GreatMesa/Bike-Led-Controller/Hardware/Microcontroller.kicad_sch

## KiCad design Hardware/Microcontroller.kicad_sch (2026-06-11)

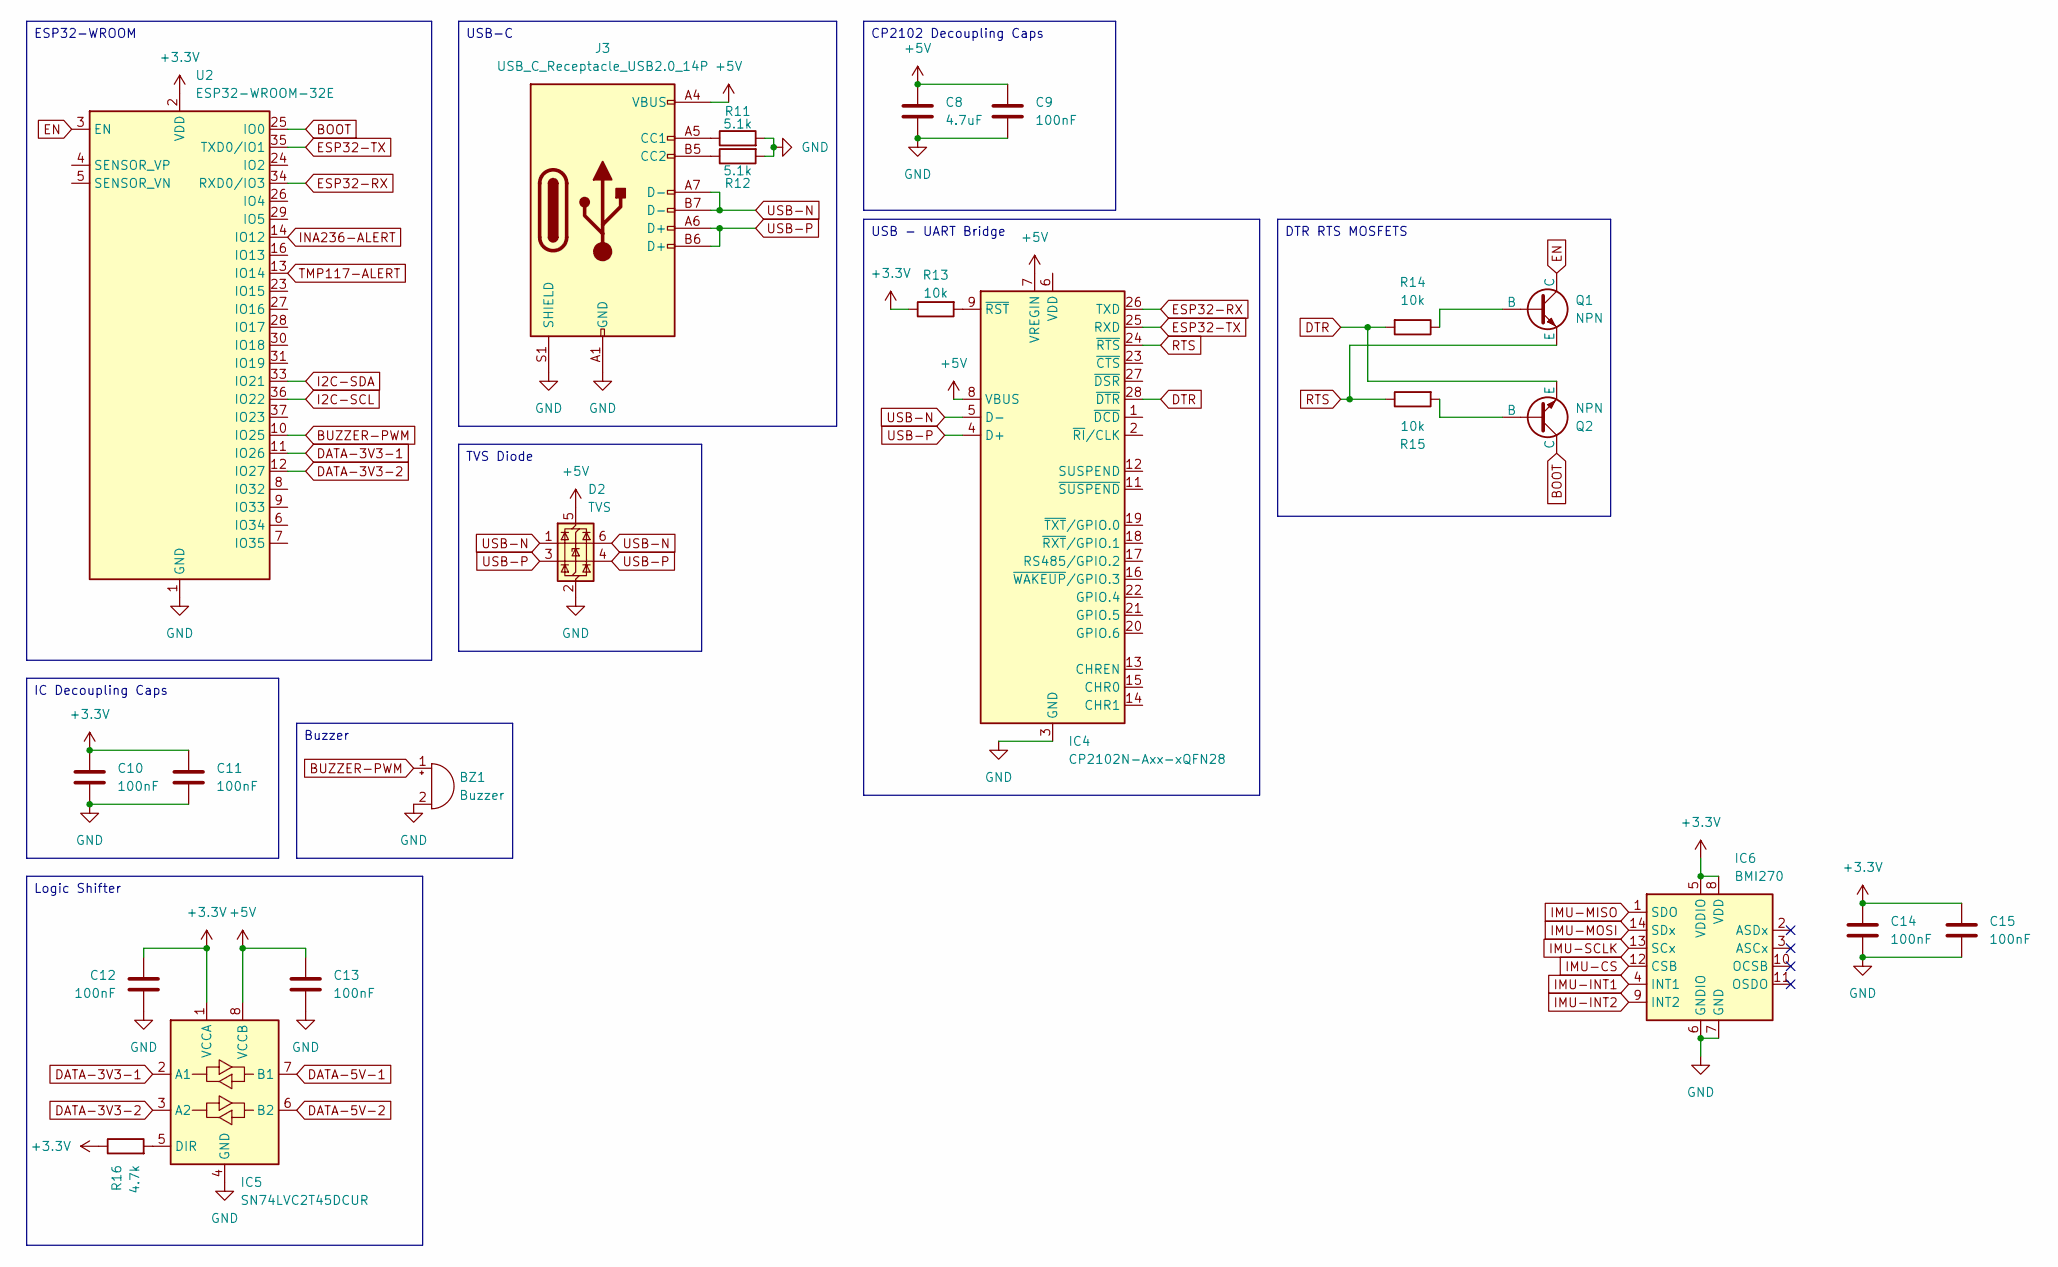
[picture p2: schematic Microcontroller.kicad_sch]

Parts:
BZ1: Buzzer; CMI97050380SMTTR
C8: 4.7uF; C_0603_1608Metric
C9, C10, C11, C12, C13, C14, C15: 100nF; C_0402_1005Metric
D2: TVS; SOT-666
IC4: CP2102N-Axx-xQFN28; QFN-28-1EP_5x5mm_P0.5mm_EP3.35x3.35mm
IC5: SN74LVC2T45DCUR; VSSOP-8_2.3x2mm_P0.5mm
IC6: BMI270; Bosch_LGA-14_3x2.5mm_P0.5mm
J3: USB_C_Receptacle_USB2.0_14P; USB_C_Receptacle_GCT_USB4105-xx-A_16P_TopMnt_Horizontal
Q1, Q2: NPN; SOT95P240X115-3N
R11, R12: 5.1k; R_0402_1005Metric
R13, R14, R15: 10k; R_0402_1005Metric
R16: 4.7k; R_0402_1005Metric
U2: ESP32-WROOM-32E

Connections:
+3.3V: C10.1, C11.1, C12.1, C14.1, C15.1, IC5.1 (VCCA), IC6.5 (VDDIO), IC6.8 (VDD), R13.1, R16.1, U2.2 (VDD)
+5V: C8.1, C9.1, C13.1, D2.5 (VBUS), IC4.7 (VREGIN), IC4.8 (VBUS), IC5.8 (VCCB), J3.A4 (VBUS), J3.A9 (VBUS), J3.B4 (VBUS), J3.B9 (VBUS)
BOOT: Q2.1 (C), U2.25 (IO0)
BUZZER-PWM: BZ1.1 (+), U2.10 (IO25)
DATA-3V3-1: IC5.2 (A1), U2.11 (IO26)
DATA-3V3-2: IC5.3 (A2), U2.12 (IO27)
DATA-5V-1: IC5.7 (B1)
DATA-5V-2: IC5.6 (B2)
DTR: IC4.28 (~DTR), Q2.3 (E), R14.2
EN: Q1.1 (C), U2.3 (EN)
ESP32-RX: IC4.26 (TXD), U2.34 (RXD0/IO3)
ESP32-TX: IC4.25 (RXD), U2.35 (TXD0/IO1)
GND: BZ1.2 (-), C8.2, C9.2, C10.2, C11.2, C12.2, C13.2, C14.2, C15.2, D2.2 (GND), IC4.3 (GND), IC4.29 (GND), IC5.4 (GND), IC6.6 (GNDIO), IC6.7 (GND), J3.A1 (GND), J3.A12 (GND), J3.B1 (GND), J3.B12 (GND), J3.S1 (SHIELD), R11.2, R12.2, U2.1 (GND), U2.15 (GND), U2.38 (GND), U2.39 (GND)
I2C-SCL: U2.36 (IO22)
I2C-SDA: U2.33 (IO21)
IMU-CS: IC6.12 (CSB)
IMU-INT1: IC6.4 (INT1)
IMU-INT2: IC6.9 (INT2)
IMU-MISO: IC6.1 (SDO)
IMU-MOSI: IC6.14 (SDx)
IMU-SCLK: IC6.13 (SCx)
INA236-ALERT: U2.14 (IO12)
unnamed: IC4.9 (~RST), R13.2
unnamed: IC5.5 (DIR), R16.2
unnamed: J3.A5 (CC1), R11.1
unnamed: J3.B5 (CC2), R12.1
unnamed: Q1.2 (B), R14.1
unnamed: Q2.2 (B), R15.2
RTS: IC4.24 (~RTS), Q1.3 (E), R15.1
TMP117-ALERT: U2.13 (IO14)
USB-N: D2.1 (I/O1), D2.6 (I/O1), IC4.5 (D-), J3.A7 (D-), J3.B7 (D-)
USB-P: D2.3 (I/O2), D2.4 (I/O2), IC4.4 (D+), J3.A6 (D+), J3.B6 (D+)

Notes on the sheet:
TVS Diode
USB-C
Logic Shifter
IC Decoupling Caps
ESP32-WROOM
USB - UART Bridge
CP2102 Decoupling Caps
DTR RTS MOSFETS
Buzzer
