GreatMesa/Bike-Led-Controller/Hardware/Power.kicad_sch

## KiCad design Hardware/Power.kicad_sch (2026-06-11)

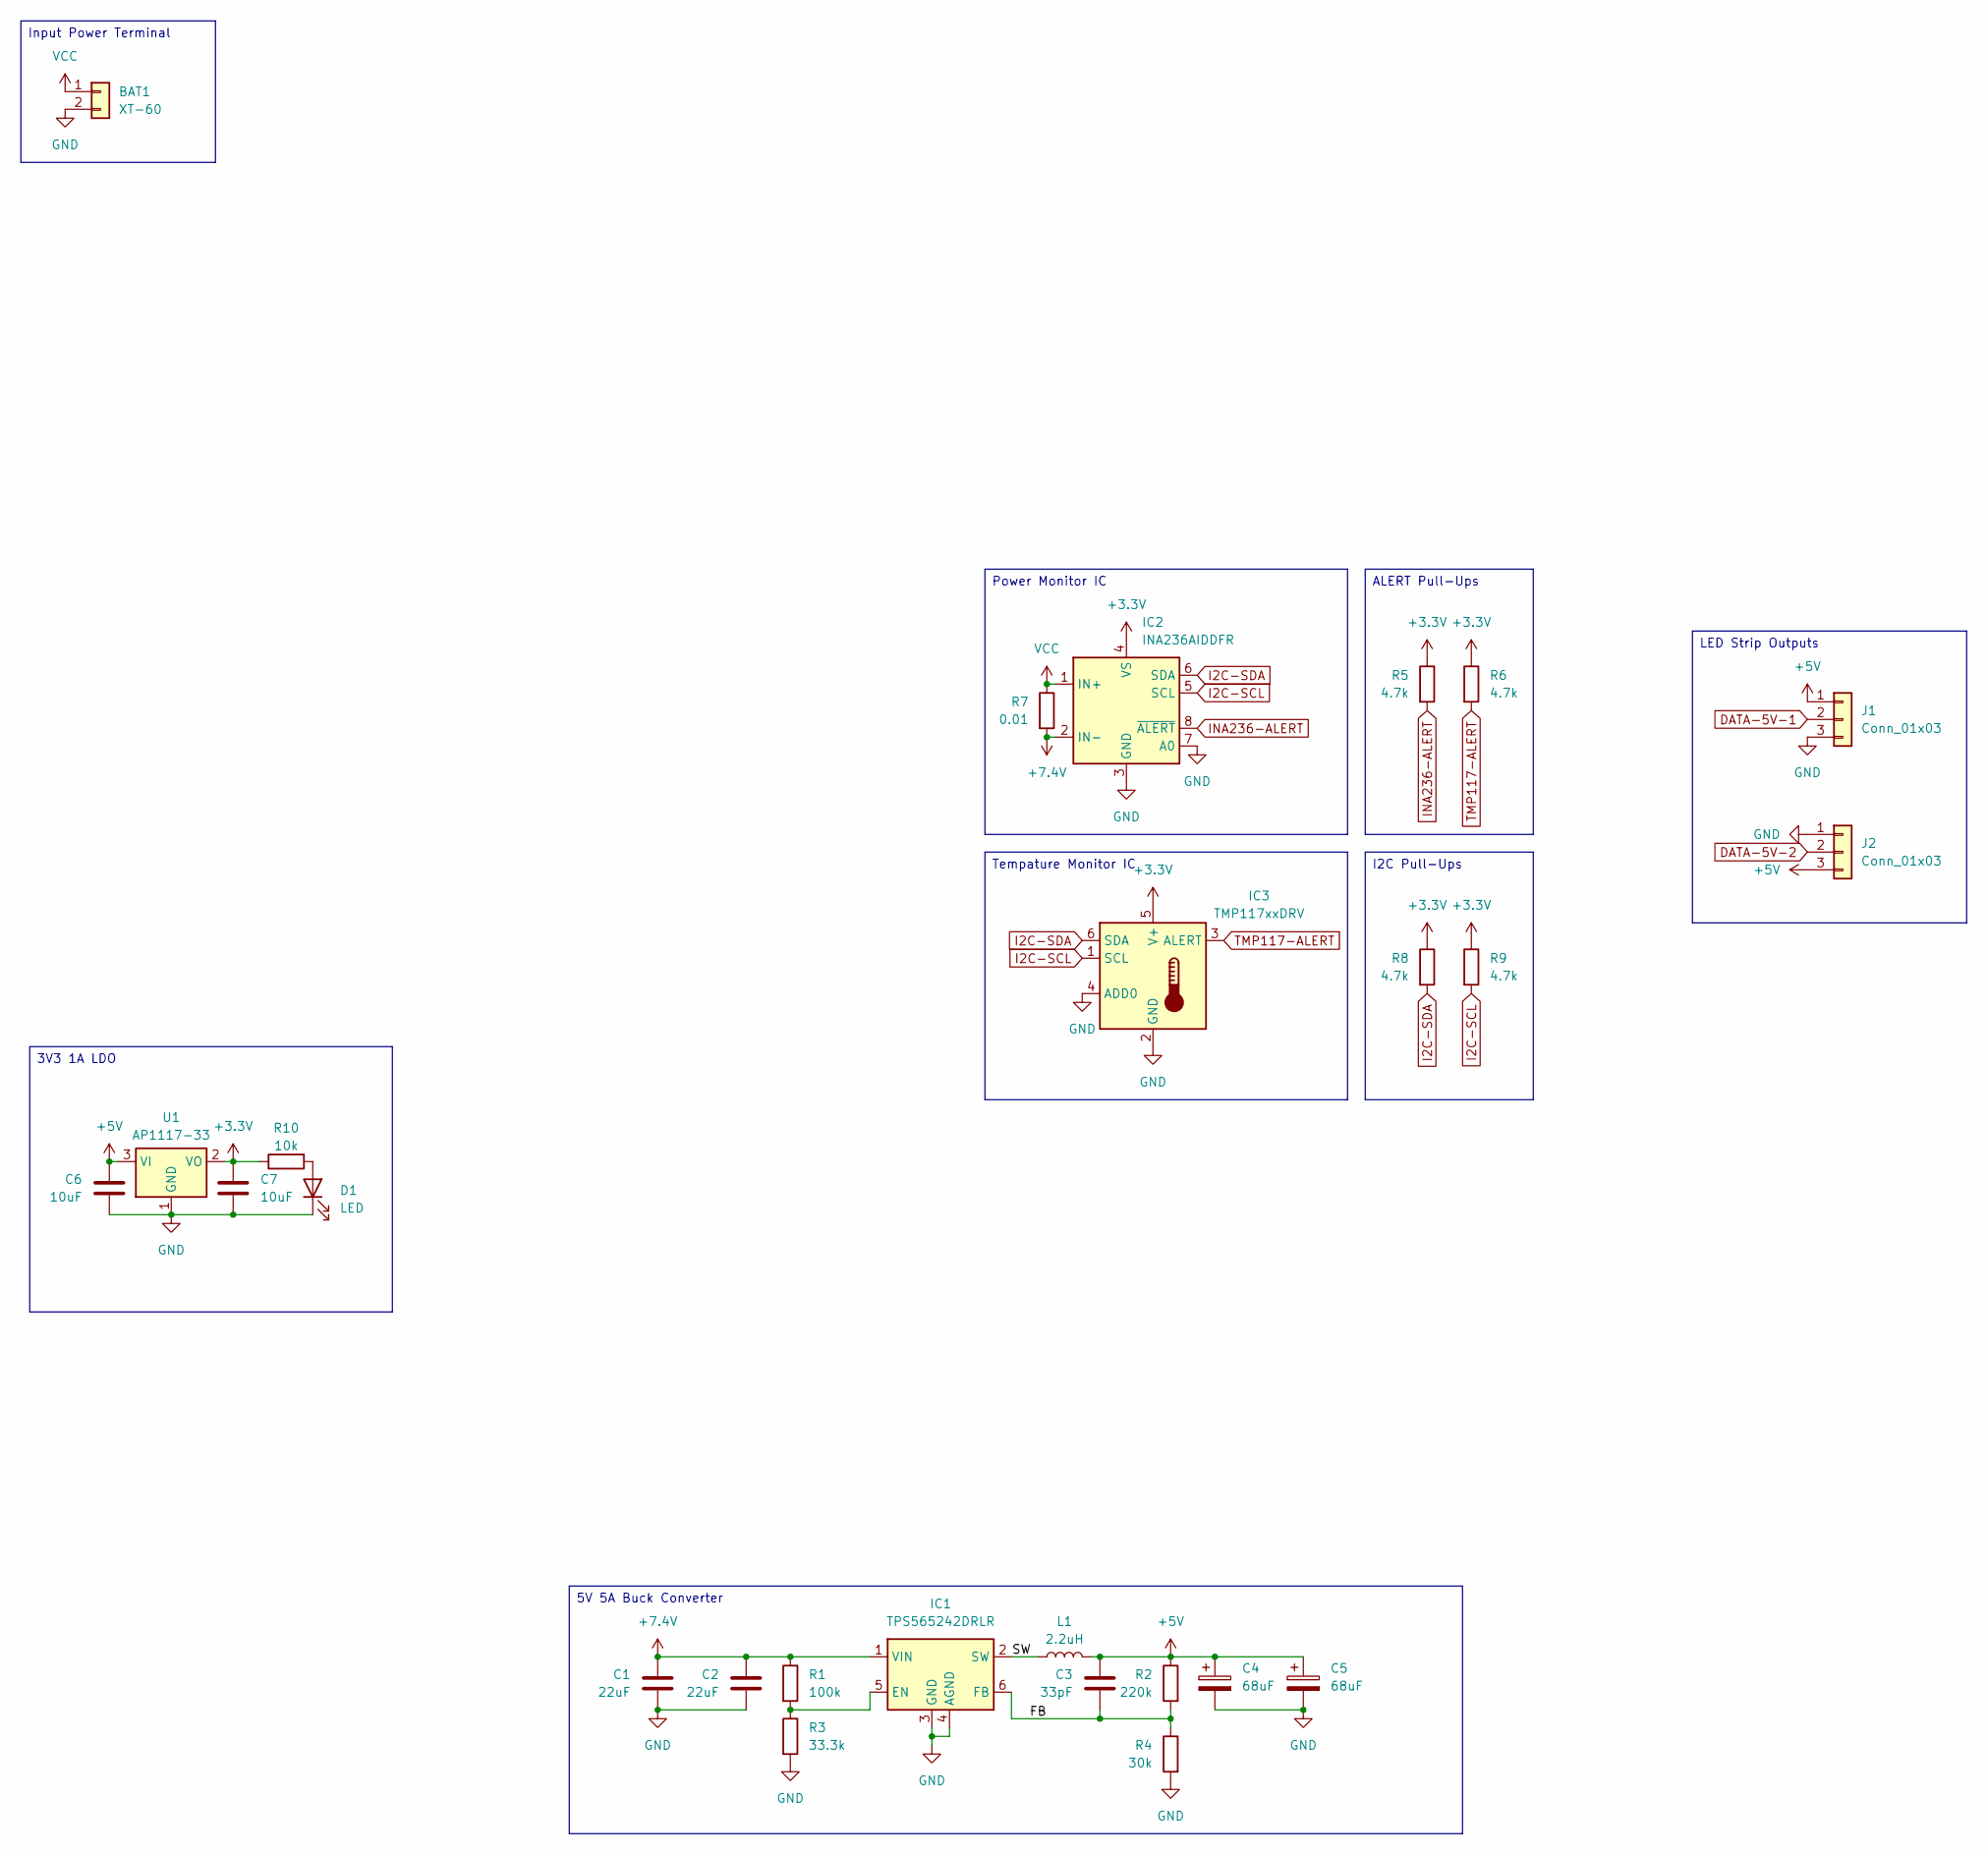
[picture p3: schematic Power.kicad_sch]

Parts:
BAT1: XT-60; AMASS_XT60-F_1x02_P7.20mm_Vertical
C1, C2: 22uF; C_0805_2012Metric
C3: 33pF; C_0402_1005Metric
C4, C5: 68uF; CP_Elec_6.3x5.8
C6, C7: 10uF; C_0805_2012Metric
D1: LED; LED_0603_1608Metric
IC1: TPS565242DRLR; SOTFL50P160X60-6N
IC2: INA236AIDDFR; SOP65P280X110-8N; Mouser Part Number 595-INA232BIDDFR
IC3: TMP117xxDRV; WSON-6-1EP_2x2mm_P0.65mm_EP1x1.6mm
J1, J2: Conn_01x03; TerminalBlock_Phoenix_MKDS-1,5-3_1x03_P5.00mm_Horizontal
L1: 2.2uH; L_Coilcraft_XAL5030-XXX
R1: 100k; R_0402_1005Metric
R2: 220k; R_0402_1005Metric
R3: 33.3k; R_0402_1005Metric
R4: 30k; R_0402_1005Metric
R5, R6, R8, R9: 4.7k; R_0402_1005Metric
R7: 0.01; R_2512_6332Metric
R10: 10k; R_0402_1005Metric
U1: AP1117-33; SOT-223-3_TabPin2

Connections:
+3.3V: C7.1, IC2.4 (VS), IC3.5 (V+), R5.1, R6.1, R8.1, R9.1, R10.1, U1.2 (VO)
+5V: C3.1, C4.1, C5.1, C6.1, J1.1, J2.3, L1.2, R2.1, U1.3 (VI)
+7.4V: C1.1, C2.1, IC1.1 (VIN), IC2.2 (IN-), R1.1, R7.2
DATA-5V-1: J1.2
DATA-5V-2: J2.2
FB: C3.2, IC1.6 (FB), R2.2, R4.1
GND: BAT1.2, C1.2, C2.2, C4.2, C5.2, C6.2, C7.2, D1.1 (K), IC1.3 (GND), IC1.4 (AGND), IC2.3 (GND), IC2.7 (A0), IC3.2 (GND), IC3.4 (ADD0), J1.3, J2.1, R3.2, R4.2, U1.1 (GND)
I2C-SCL: IC2.5 (SCL), IC3.1 (SCL), R9.2
I2C-SDA: IC2.6 (SDA), IC3.6 (SDA), R8.2
INA236-ALERT: IC2.8 (~ALERT), R5.2
unnamed: D1.2 (A), R10.2
unnamed: IC1.5 (EN), R1.2, R3.1
SW: IC1.2 (SW), L1.1
TMP117-ALERT: IC3.3 (ALERT), R6.2
VCC: BAT1.1, IC2.1 (IN+), R7.1

Notes on the sheet:
Power Monitor IC
3V3 1A LDO
I2C Pull-Ups
LED Strip Outputs
ALERT Pull-Ups
Tempature Monitor IC
Input Power Terminal
5V 5A Buck Converter
