GreatMesa/Bike-Led-Controller/Hardware/WLED Controller.kicad_sch

## KiCad design Hardware/WLED Controller.kicad_sch (2026-06-11)

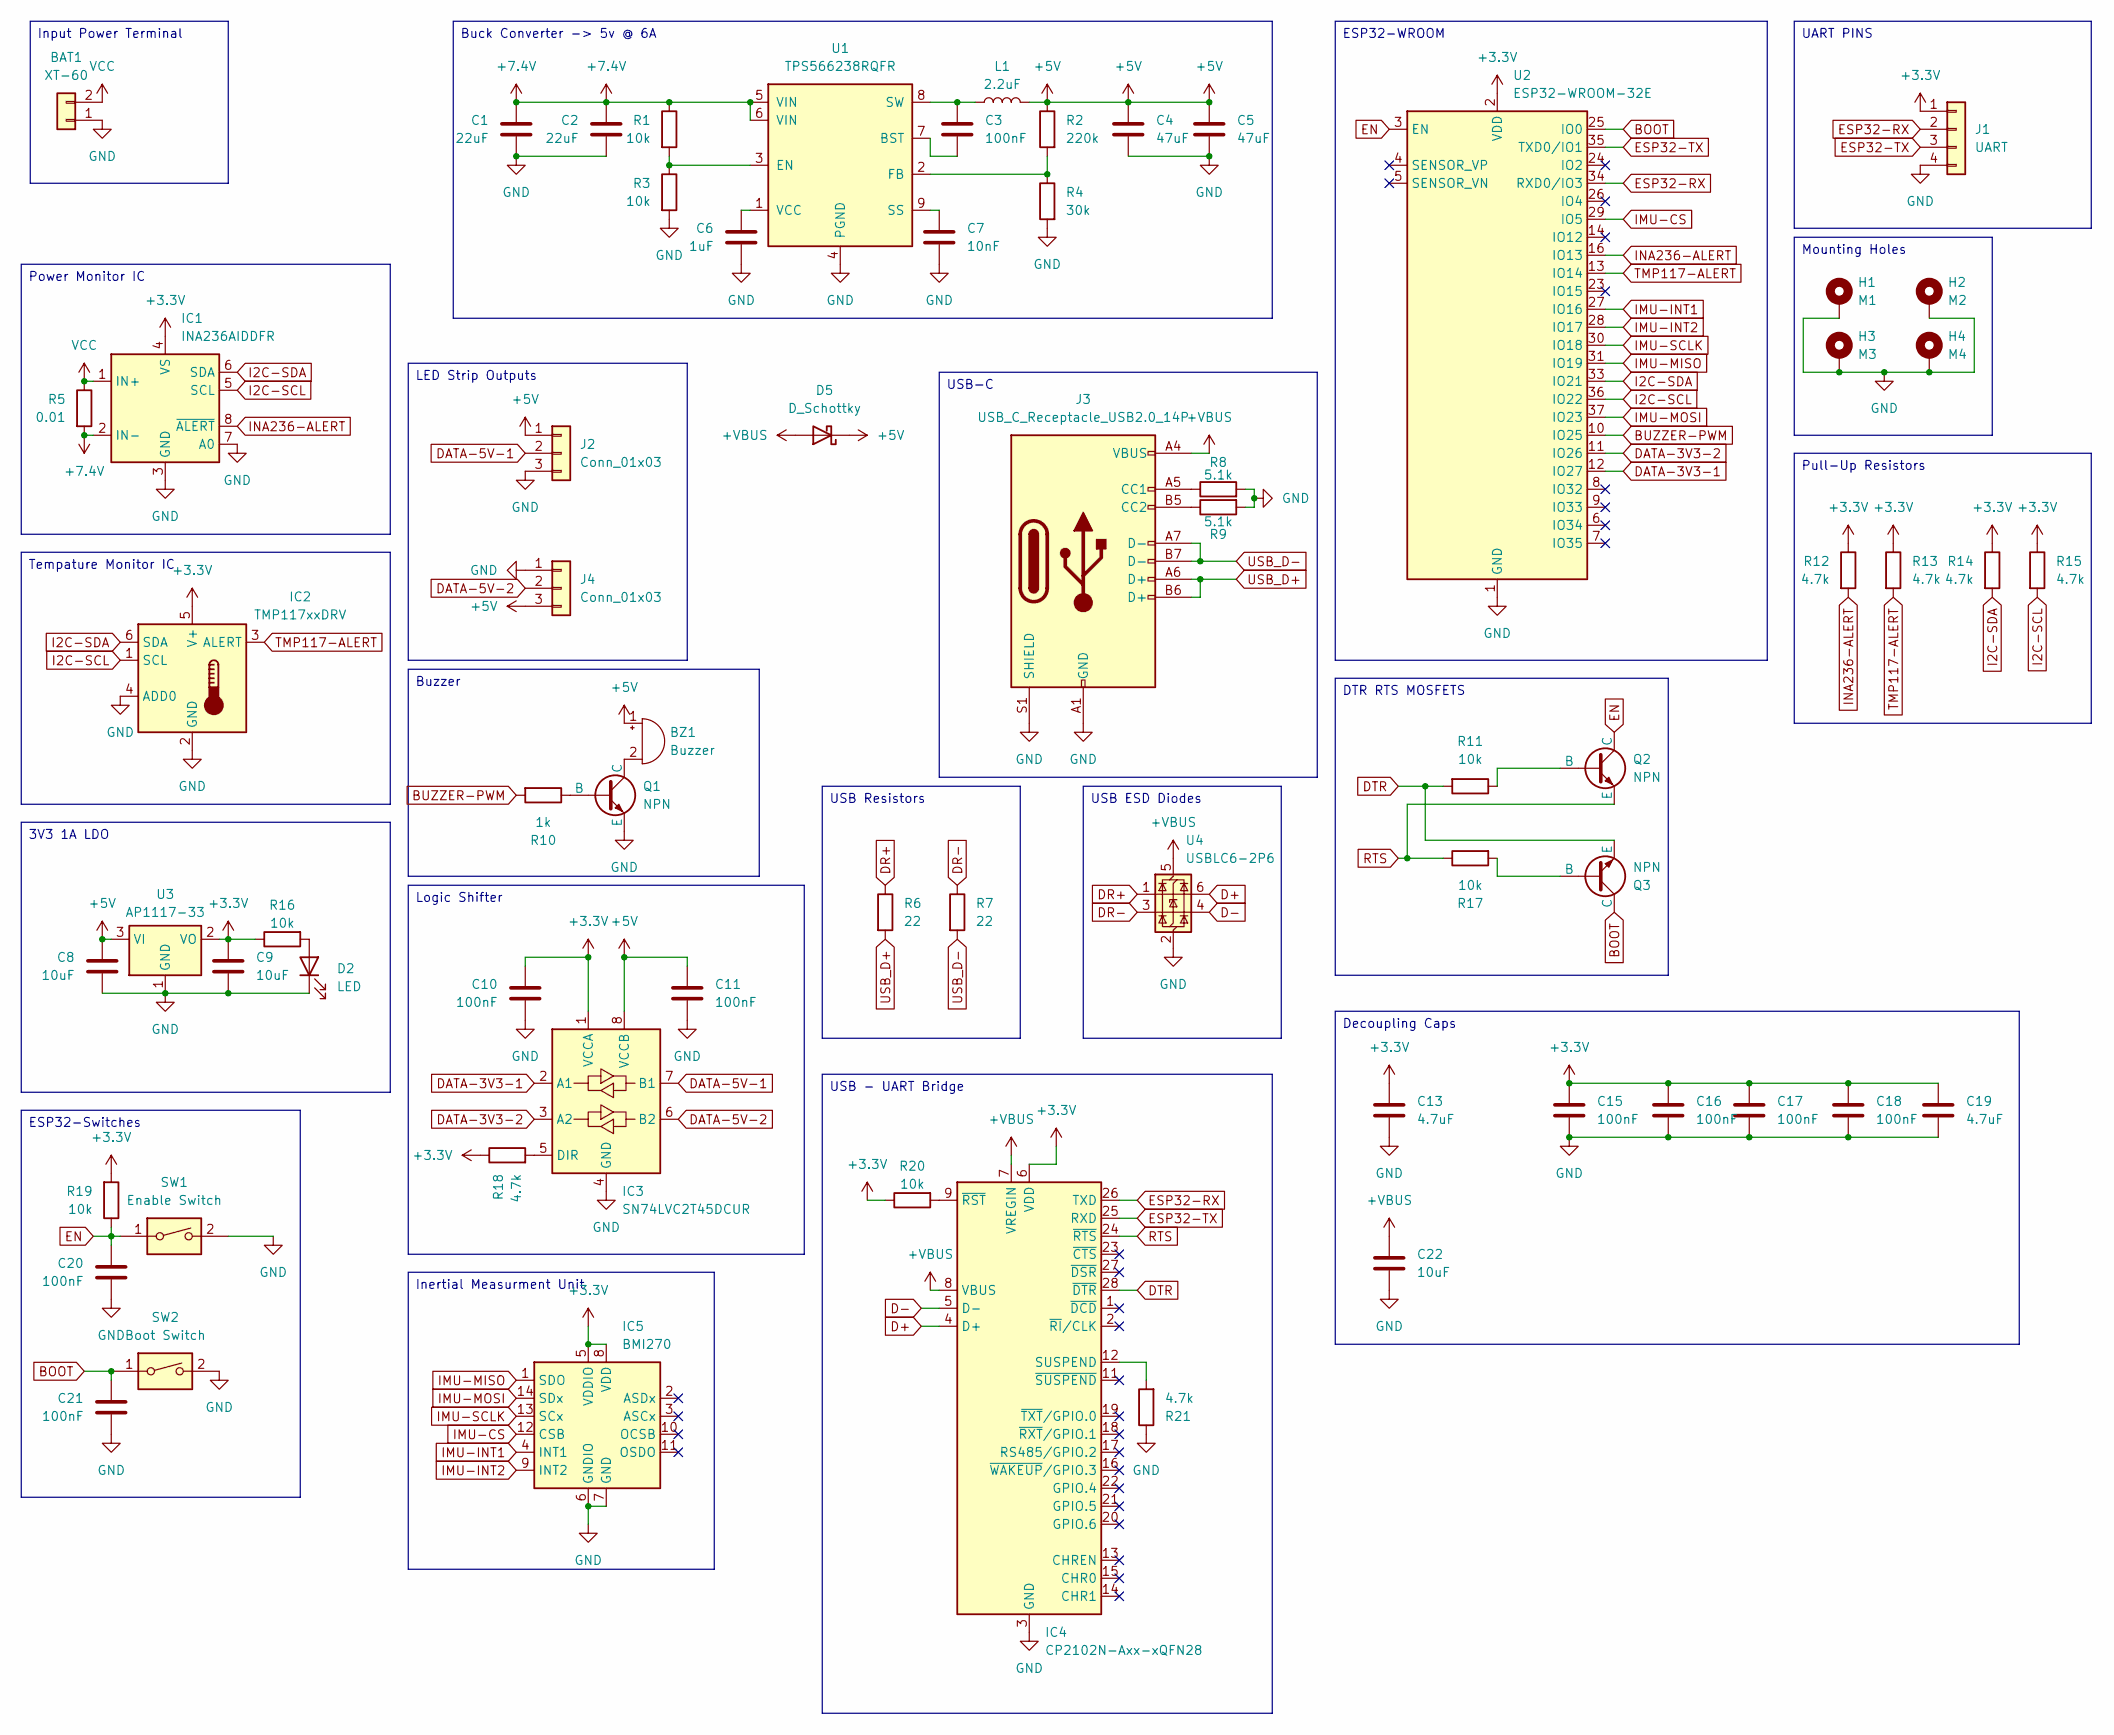
[picture p4: schematic WLED Controller.kicad_sch]

Parts:
BAT1: XT-60; AMASS_XT60-F_1x02_P7.20mm_Vertical
BZ1: Buzzer; CMI97050380SMTTR
C1, C2: 22uF; C_1206_3216Metric
C3, C10, C11, C15, C16, C17, C18, C20, C21: 100nF; C_0402_1005Metric
C4, C5: 47uF; C_1210_3225Metric
C6: 1uF; C_0402_1005Metric
C7: 10nF; C_0402_1005Metric
C8, C9: 10uF; C_0805_2012Metric
C13, C19: 4.7uF; C_0603_1608Metric
C22: 10uF; C_0603_1608Metric
D2: LED; LED_0603_1608Metric
D5: D_Schottky; D_0603_1608Metric
H1: M1; MountingHole_3.2mm_M3_Pad_Via
H2: M2; MountingHole_3.2mm_M3_Pad_Via
H3: M3; MountingHole_3.2mm_M3_Pad_Via
H4: M4; MountingHole_3.2mm_M3_Pad_Via
IC1: INA236AIDDFR; SOP65P280X110-8N; Mouser Part Number 595-INA232BIDDFR
IC2: TMP117xxDRV; WSON-6-1EP_2x2mm_P0.65mm_EP1x1.6mm
IC3: SN74LVC2T45DCUR; VSSOP-8_2.3x2mm_P0.5mm
IC4: CP2102N-Axx-xQFN28; QFN-28-1EP_5x5mm_P0.5mm_EP3.35x3.35mm
IC5: BMI270; Bosch_LGA-14_3x2.5mm_P0.5mm
J1: UART; PinSocket_1x04_P2.54mm_Vertical
J2, J4: Conn_01x03; TerminalBlock_Phoenix_MKDS-1,5-3_1x03_P5.00mm_Horizontal
J3: USB_C_Receptacle_USB2.0_14P; USB_C_Receptacle_GCT_USB4105-xx-A_16P_TopMnt_Horizontal
L1: 2.2uF; L_Coilcraft_XAL6030-XXX
Q1, Q2, Q3: NPN; SOT95P240X115-3N
R1, R3, R11, R17, R19, R20: 10k; R_0402_1005Metric
R2: 220k; R_0402_1005Metric
R4: 30k; R_0402_1005Metric
R5: 0.01; R_2512_6332Metric
R6, R7: 22; R_0402_1005Metric
R8, R9: 5.1k; R_0402_1005Metric
R10: 1k; R_0402_1005Metric
R12, R13, R14, R15, R18, R21: 4.7k; R_0402_1005Metric
R16: 10k; R_0603_1608Metric
SW1: Enable Switch; SW_SPST_TS-1088-xR025
SW2: Boot Switch; SW_SPST_TS-1088-xR025
U1: TPS566238RQFR; PARTREV A
U2: ESP32-WROOM-32E
U3: AP1117-33; SOT-223-3_TabPin2
U4: USBLC6-2P6; SOT-666

Connections:
+3.3V: C9.1, C10.1, C13.1, C15.1, C16.1, C17.1, C18.1, C19.1, IC1.4 (VS), IC2.5 (V+), IC3.1 (VCCA), IC4.6 (VDD), IC5.5 (VDDIO), IC5.8 (VDD), J1.1, R12.1, R13.1, R14.1, R15.1, R16.1, R18.1, R19.2, R20.1, U2.2 (VDD), U3.2 (VO)
+5V: BZ1.1 (+), C4.1, C5.1, C8.1, C11.1, D5.1 (K), IC3.8 (VCCB), J2.1, J4.3, L1.2, R2.1, U3.3 (VI)
+7.4V: C1.1, C2.1, IC1.2 (IN-), R1.1, R5.2, U1.5 (VIN), U1.6 (VIN)
+VBUS: C22.1, D5.2 (A), IC4.7 (VREGIN), IC4.8 (VBUS), J3.A4 (VBUS), J3.A9 (VBUS), J3.B4 (VBUS), J3.B9 (VBUS), U4.5 (VBUS)
BOOT: C21.1, Q3.1 (C), SW2.1, U2.25 (IO0)
BUZZER-PWM: R10.2, U2.10 (IO25)
D+: IC4.4 (D+), U4.6 (I/O1)
D-: IC4.5 (D-), U4.4 (I/O2)
DATA-3V3-1: IC3.2 (A1), U2.12 (IO27)
DATA-3V3-2: IC3.3 (A2), U2.11 (IO26)
DATA-5V-1: IC3.7 (B1), J2.2
DATA-5V-2: IC3.6 (B2), J4.2
DR+: R6.1, U4.1 (I/O1)
DR-: R7.1, U4.3 (I/O2)
DTR: IC4.28 (~DTR), Q3.3 (E), R11.2
EN: C20.1, Q2.1 (C), R19.1, SW1.1, U2.3 (EN)
ESP32-RX: IC4.26 (TXD), J1.2, U2.34 (RXD0/IO3)
ESP32-TX: IC4.25 (RXD), J1.3, U2.35 (TXD0/IO1)
GND: BAT1.1, C1.2, C2.2, C4.2, C5.2, C6.1, C7.1, C8.2, C9.2, C10.2, C11.2, C13.2, C15.2, C16.2, C17.2, C18.2, C19.2, C20.2, C21.2, C22.2, D2.1 (K), H1.1, H2.1, H3.1, H4.1, IC1.3 (GND), IC1.7 (A0), IC2.2 (GND), IC2.4 (ADD0), IC3.4 (GND), IC4.3 (GND), IC4.29 (GND), IC5.6 (GNDIO), IC5.7 (GND), J1.4, J2.3, J3.A1 (GND), J3.A12 (GND), J3.B1 (GND), J3.B12 (GND), J3.S1 (SHIELD), J4.1, Q1.3 (E), R3.2, R4.2, R8.2, R9.2, R21.1, SW1.2, SW2.2, U1.4 (PGND), U2.1 (GND), U2.15 (GND), U2.38 (GND), U2.39 (GND), U3.1 (GND), U4.2 (GND)
I2C-SCL: IC1.5 (SCL), IC2.1 (SCL), R15.2, U2.36 (IO22)
I2C-SDA: IC1.6 (SDA), IC2.6 (SDA), R14.2, U2.33 (IO21)
IMU-CS: IC5.12 (CSB), U2.29 (IO5)
IMU-INT1: IC5.4 (INT1), U2.27 (IO16)
IMU-INT2: IC5.9 (INT2), U2.28 (IO17)
IMU-MISO: IC5.1 (SDO), U2.31 (IO19)
IMU-MOSI: IC5.14 (SDx), U2.37 (IO23)
IMU-SCLK: IC5.13 (SCx), U2.30 (IO18)
INA236-ALERT: IC1.8 (~ALERT), R12.2, U2.16 (IO13)
unnamed: BZ1.2 (-), Q1.1 (C)
unnamed: C3.1, U1.7 (BST)
unnamed: C3.2, L1.1, U1.8 (SW)
unnamed: C6.2, U1.1 (VCC)
unnamed: C7.2, U1.9 (SS)
unnamed: D2.2 (A), R16.2
unnamed: IC3.5 (DIR), R18.2
unnamed: IC4.9 (~RST), R20.2
unnamed: IC4.12 (SUSPEND), R21.2
unnamed: J3.A5 (CC1), R8.1
unnamed: J3.B5 (CC2), R9.1
unnamed: Q1.2 (B), R10.1
unnamed: Q2.2 (B), R11.1
unnamed: Q3.2 (B), R17.2
unnamed: R1.2, R3.1, U1.3 (EN)
unnamed: R2.2, R4.1, U1.2 (FB)
RTS: IC4.24 (~RTS), Q2.3 (E), R17.1
TMP117-ALERT: IC2.3 (ALERT), R13.2, U2.13 (IO14)
USB_D+: J3.A6 (D+), J3.B6 (D+), R6.2
USB_D-: J3.A7 (D-), J3.B7 (D-), R7.2
VCC: BAT1.2, IC1.1 (IN+), R5.1

Notes on the sheet:
Pull-Up Resistors
ESP32-WROOM
ESP32-Switches
USB-C
LED Strip Outputs
Buck Converter -> 5v @ 6A
Logic Shifter
USB - UART Bridge
DTR RTS MOSFETS
3V3 1A LDO
Tempature Monitor IC
Buzzer
USB ESD Diodes
Power Monitor IC
UART PINS
Inertial Measurment Unit
Decoupling Caps
USB Resistors
Input Power Terminal
Mounting Holes
